Rogger/schneggi-sensor/include/app_measurement_logic.h

#ifndef APP_MEASUREMENT_LOGIC_H_
#define APP_MEASUREMENT_LOGIC_H_

#include <stdbool.h>
#include <stdint.h>

bool app_report_due_s16(bool valid,
			int16_t previous_value,
			uint32_t previous_cycle,
			int16_t new_value,
			int16_t threshold,
			uint32_t current_cycle,
			uint32_t refresh_cycles);

unsigned int app_battery_level_pptt(unsigned int batt_mv);
int32_t app_battery_millivolts_from_adc(int32_t adc_mv);
uint8_t app_battery_voltage_zcl_attribute(int32_t battery_mv);
uint8_t app_battery_percentage_from_mv(uint32_t battery_mv);
uint8_t app_battery_percentage_zcl_attribute(uint8_t percentage);

#endif /* APP_MEASUREMENT_LOGIC_H_ */
